plocher/Brakeman/Fabricated.jpg

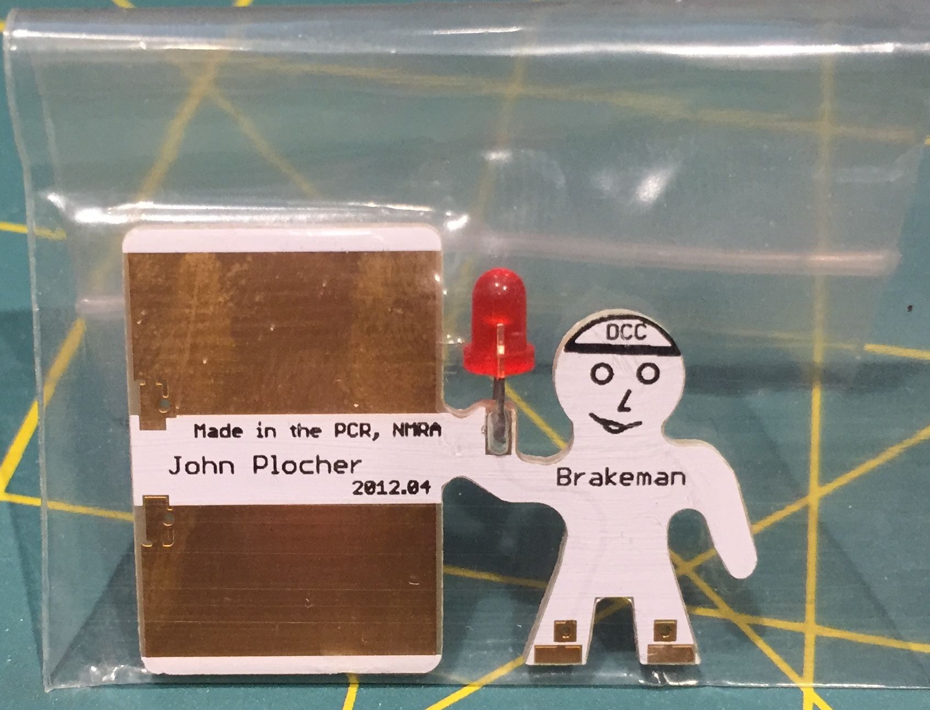
Fabricated.jpg
